AlbertGBarber/Pixel-Shades/Images/IMG_20191211_094721 (1).jpg

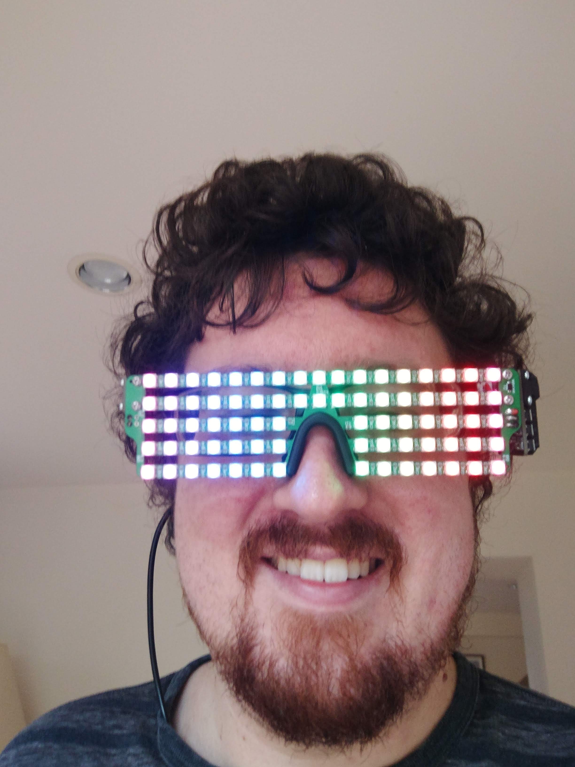
Images/IMG_20191211_094721 (1).jpg
