AlbertGBarber/Pixel-Shades/Images/Shades Back.jpg

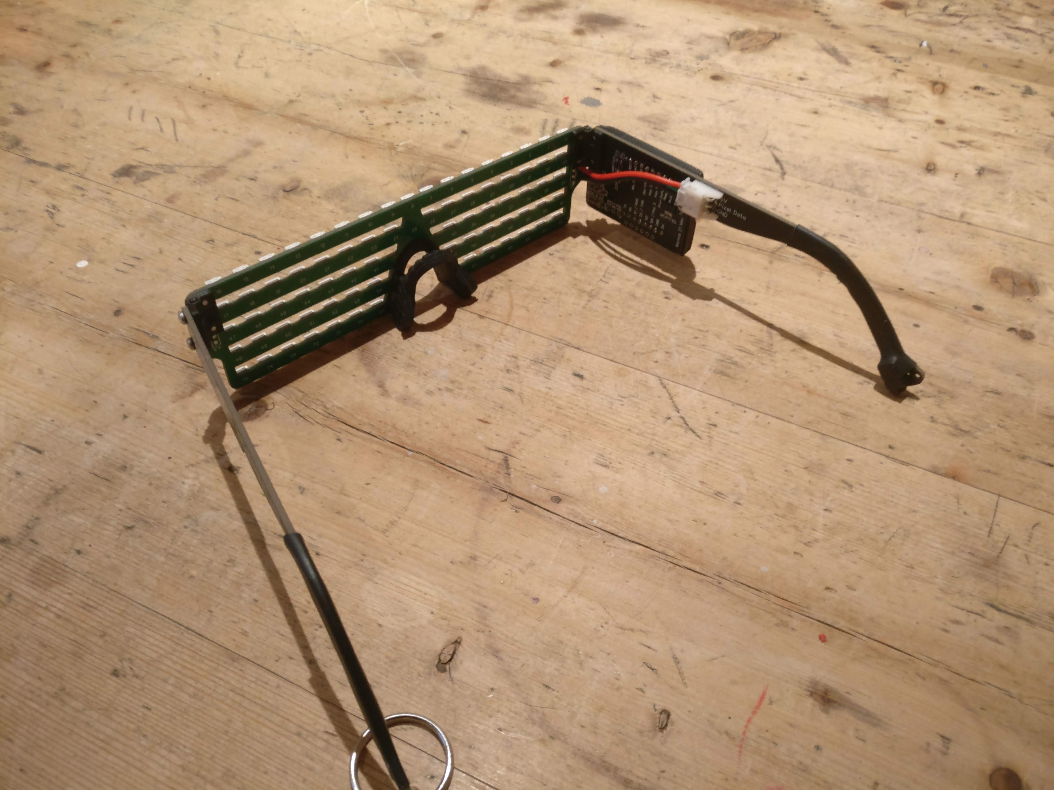
Images/Shades Back.jpg
