AlbertGBarber/Pixel-Shades/Images/Shades Cover.jpg

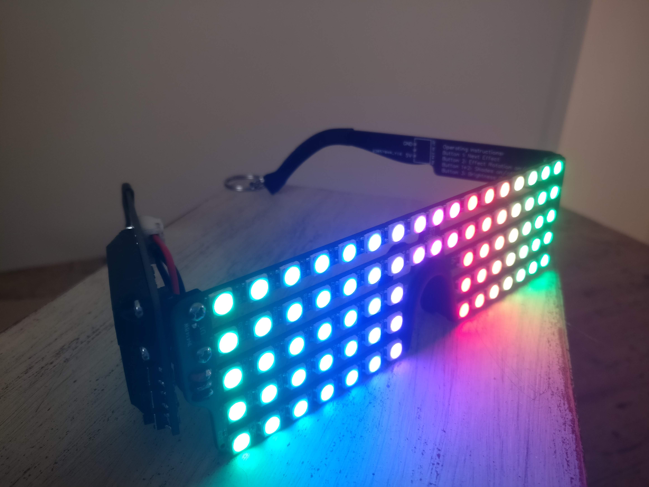
Images/Shades Cover.jpg
