AlbertGBarber/Pixel-Shades/Images/Shades PCBs and Power Bank.jpg

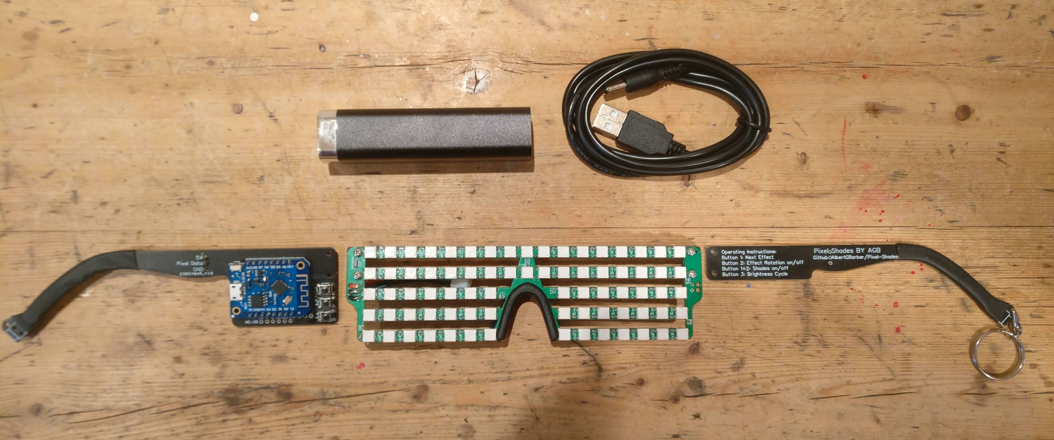
Images/Shades PCBs and Power Bank.jpg
