AlbertGBarber/Pixel-Shades/Images/Shades With Power Bank - Copy.jpg

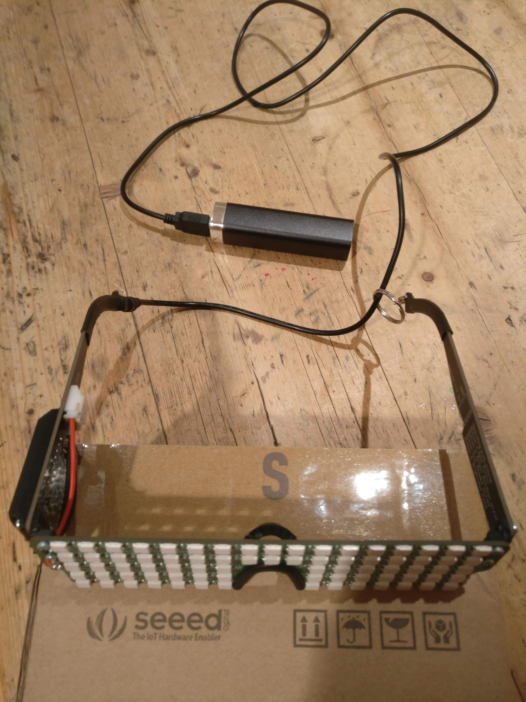
Images/Shades With Power Bank - Copy.jpg
