AlbertGBarber/Pixel-Shades/Images/PCB Ordering 2.PNG

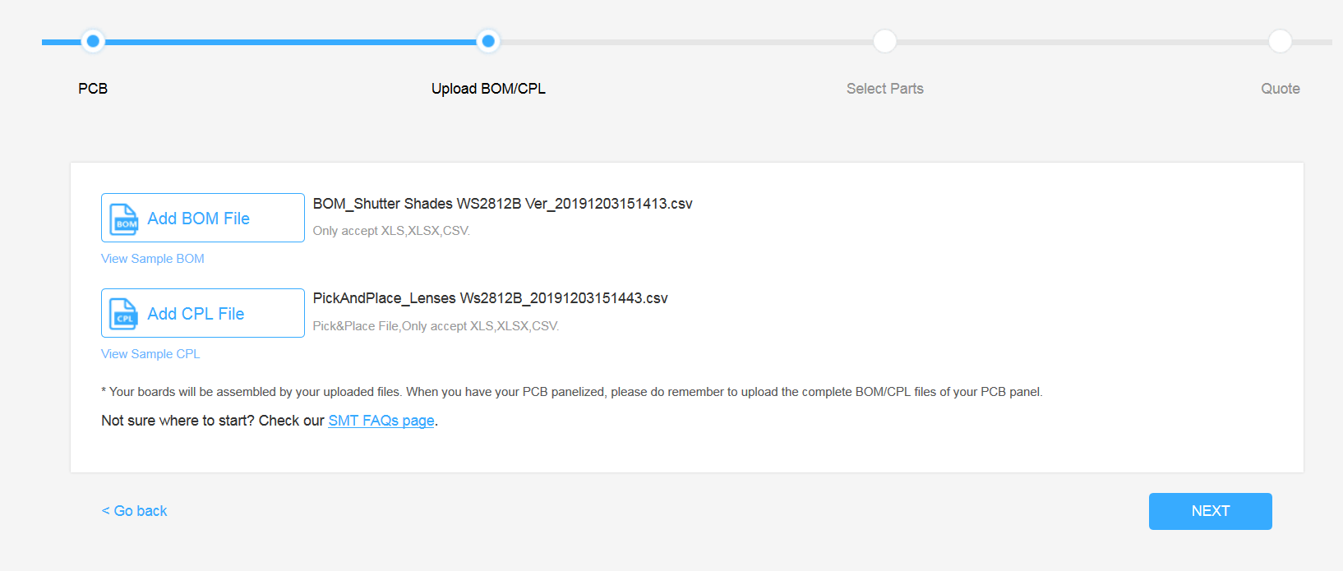
Images/PCB Ordering 2.PNG
