AlbertGBarber/Pixel-Shades/Images/PCB Ordering 4.PNG

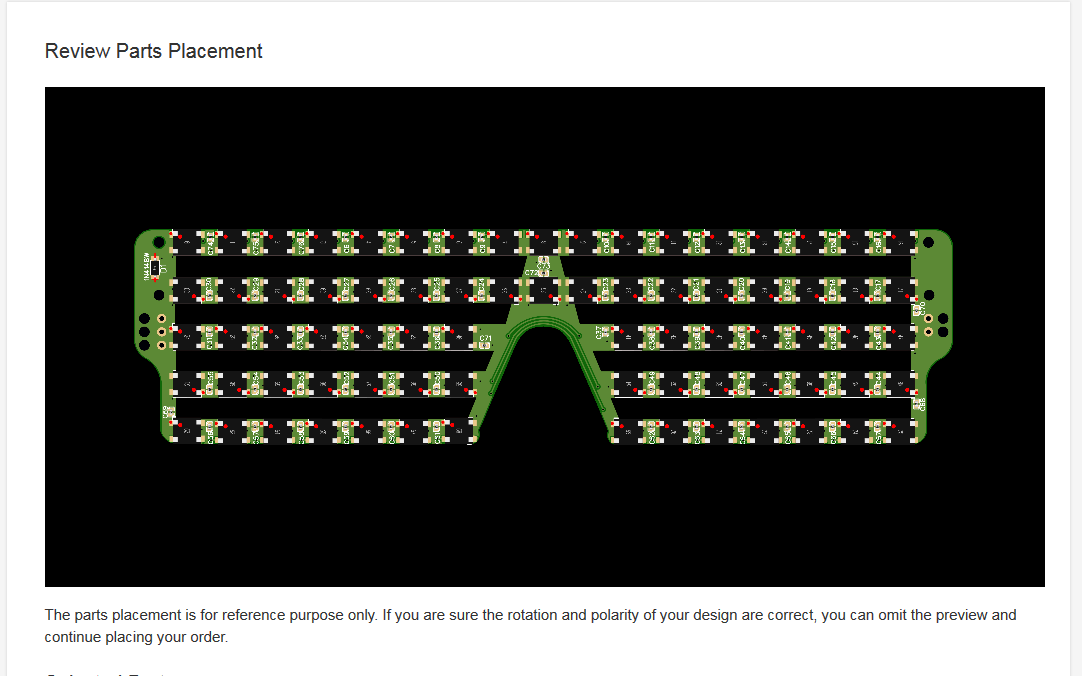
Images/PCB Ordering 4.PNG
