AlbertGBarber/Pixel-Shades/Images/Shades Final Assemble 1.jpg

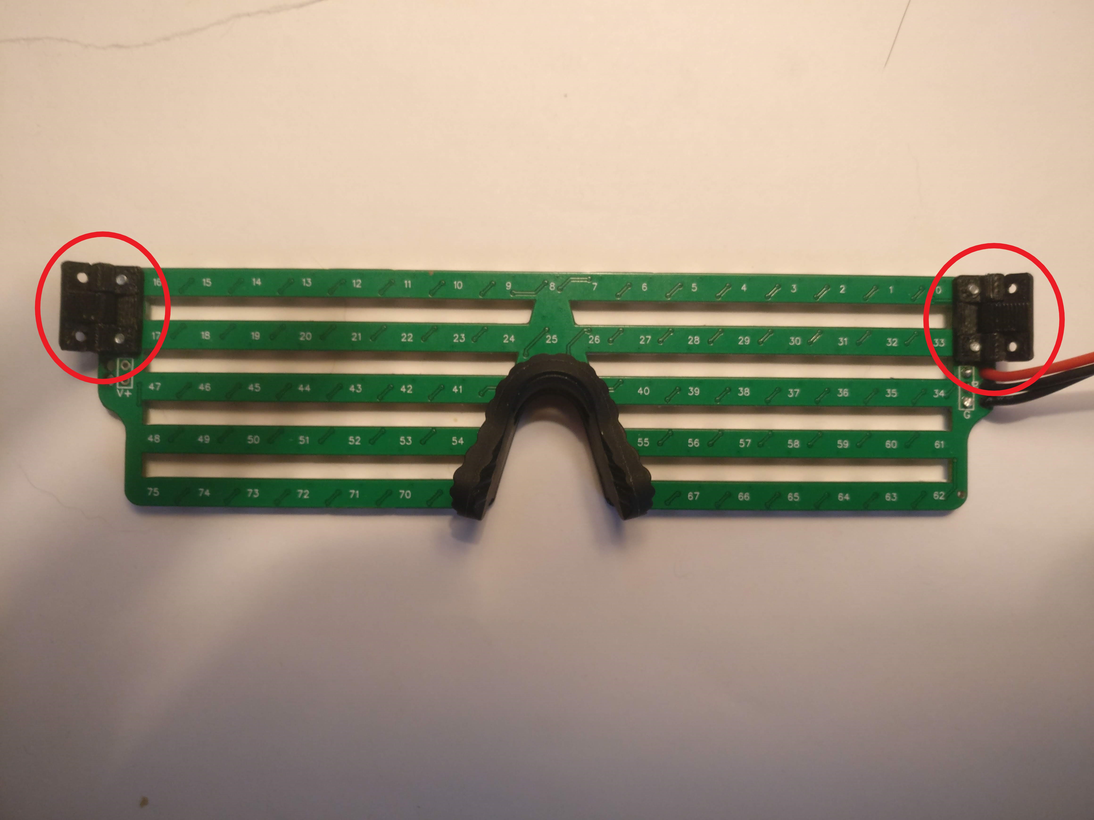
Images/Shades Final Assemble 1.jpg
