AlbertGBarber/Pixel-Shades/Images/Shades Final Assemble 2.jpg

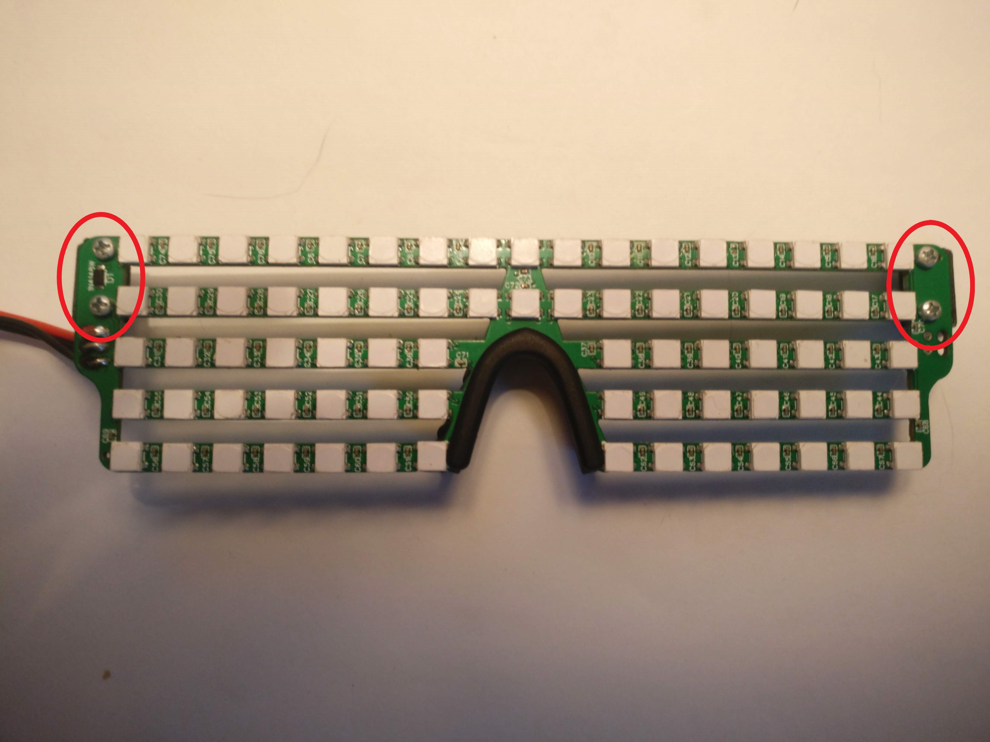
Images/Shades Final Assemble 2.jpg
