AlbertGBarber/Pixel-Shades/Images/Shades Final Assemble 3.jpg

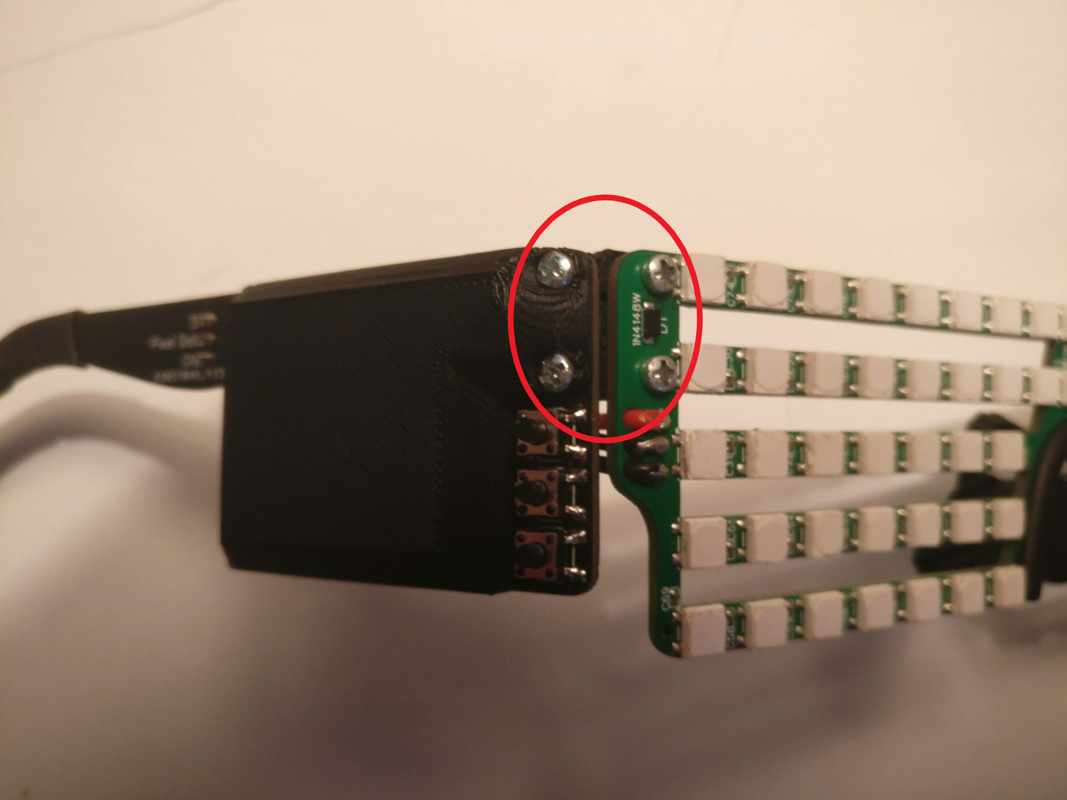
Images/Shades Final Assemble 3.jpg
