AlbertGBarber/Pixel-Shades/Images/Shades Final Assemble 5.jpg

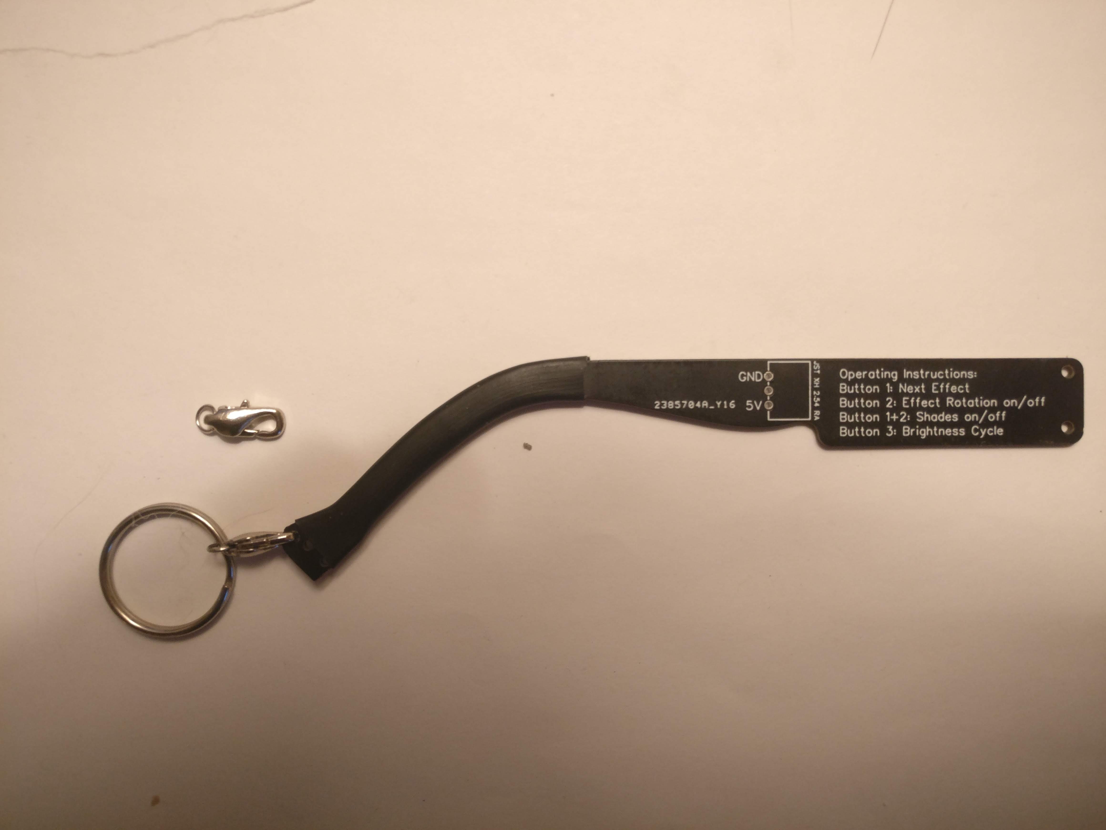
Images/Shades Final Assemble 5.jpg
