AlbertGBarber/Pixel-Shades/Images/Shades Final Assemble 6.jpg

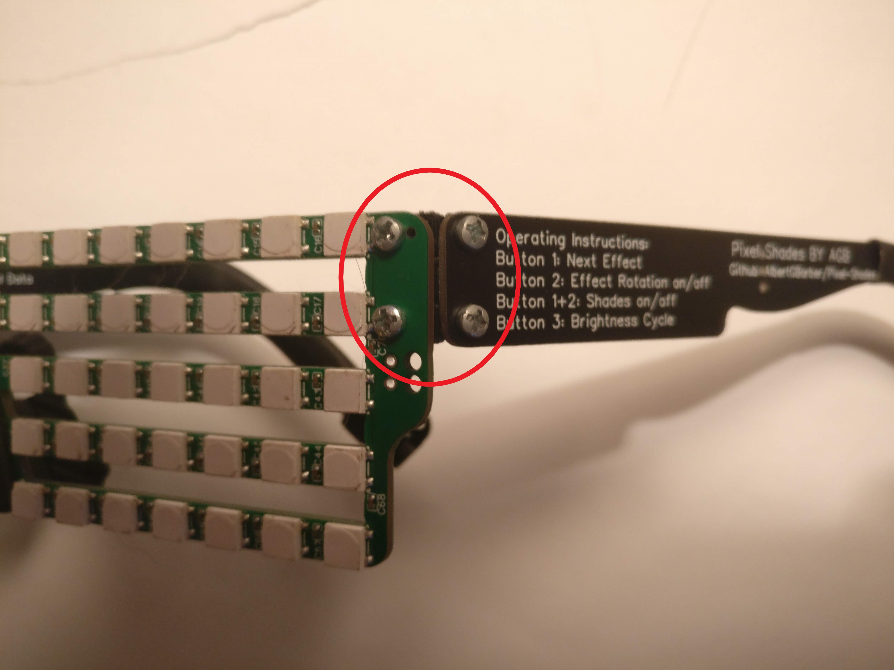
Images/Shades Final Assemble 6.jpg
