AlbertGBarber/Pixel-Shades/Images/Shades Final Assemble 8.PNG

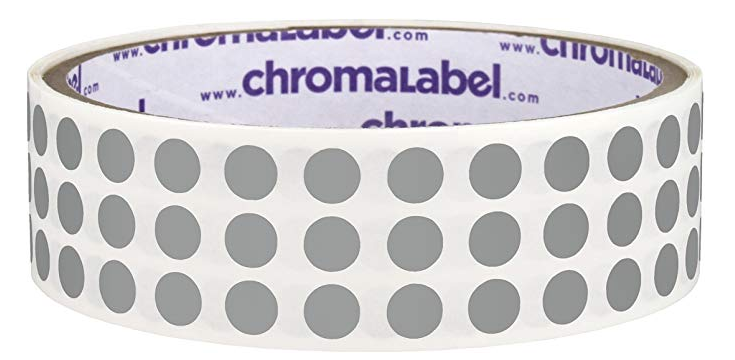
Images/Shades Final Assemble 8.PNG
