AlbertGBarber/Pixel-Shades/Images/Shades PCB Assembly 1.jpg

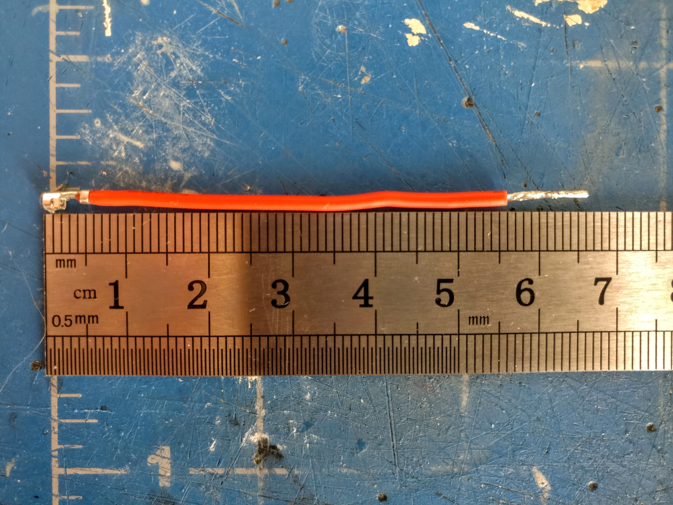
Images/Shades PCB Assembly 1.jpg
