AlbertGBarber/Pixel-Shades/Images/Shades PCB Assembly 2.jpg

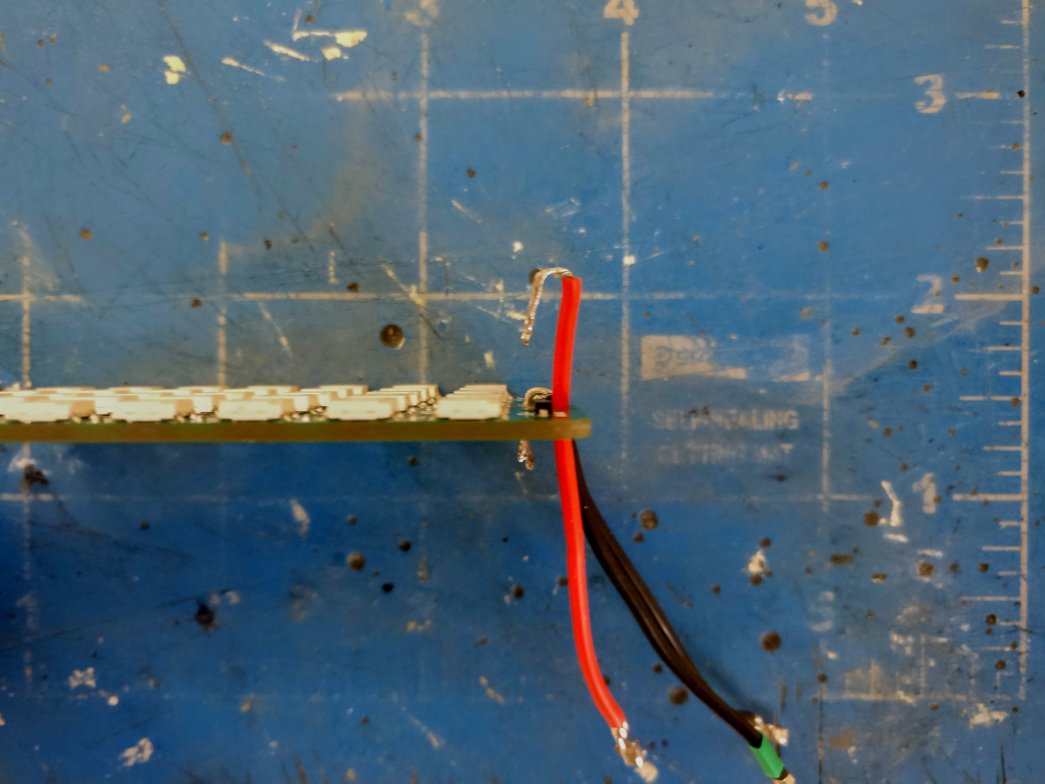
Images/Shades PCB Assembly 2.jpg
