AlbertGBarber/Pixel-Shades/Images/Shades PCB Assembly 3.jpg

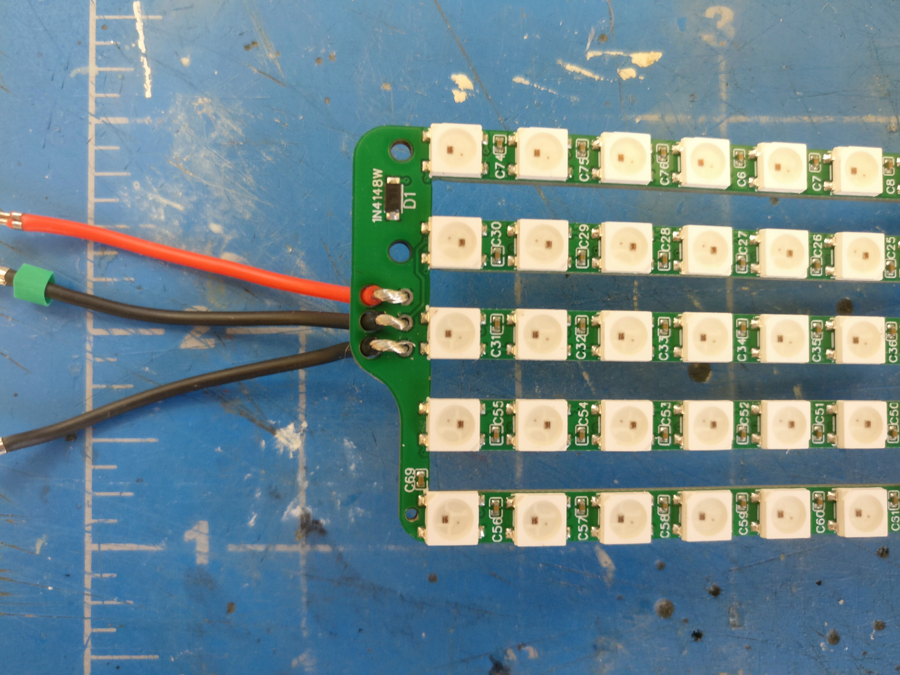
Images/Shades PCB Assembly 3.jpg
