AlbertGBarber/Pixel-Shades/Images/Shades PCB Assembly 4.jpg

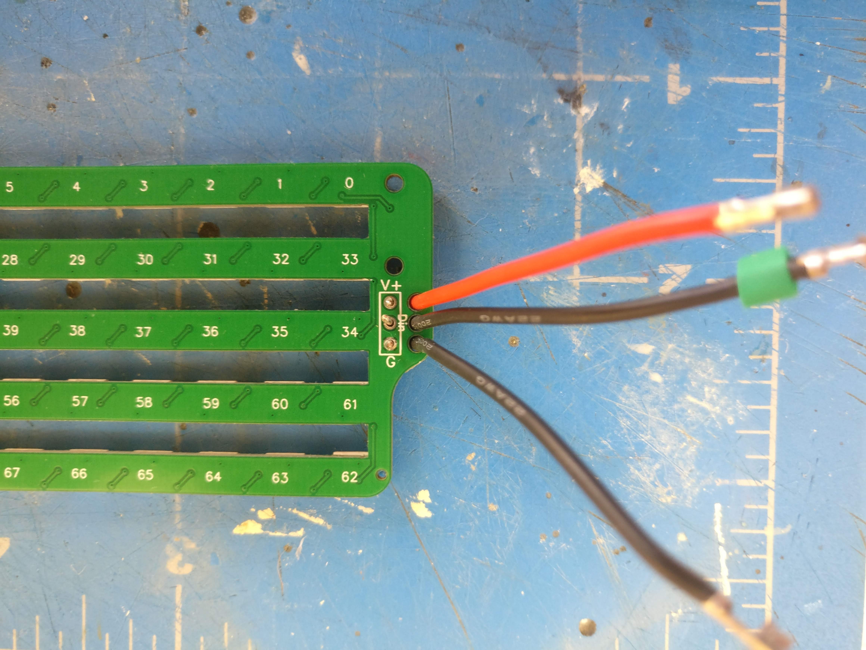
Images/Shades PCB Assembly 4.jpg
