AlbertGBarber/Pixel-Shades/Images/Shades PCB Assembly 5.jpg

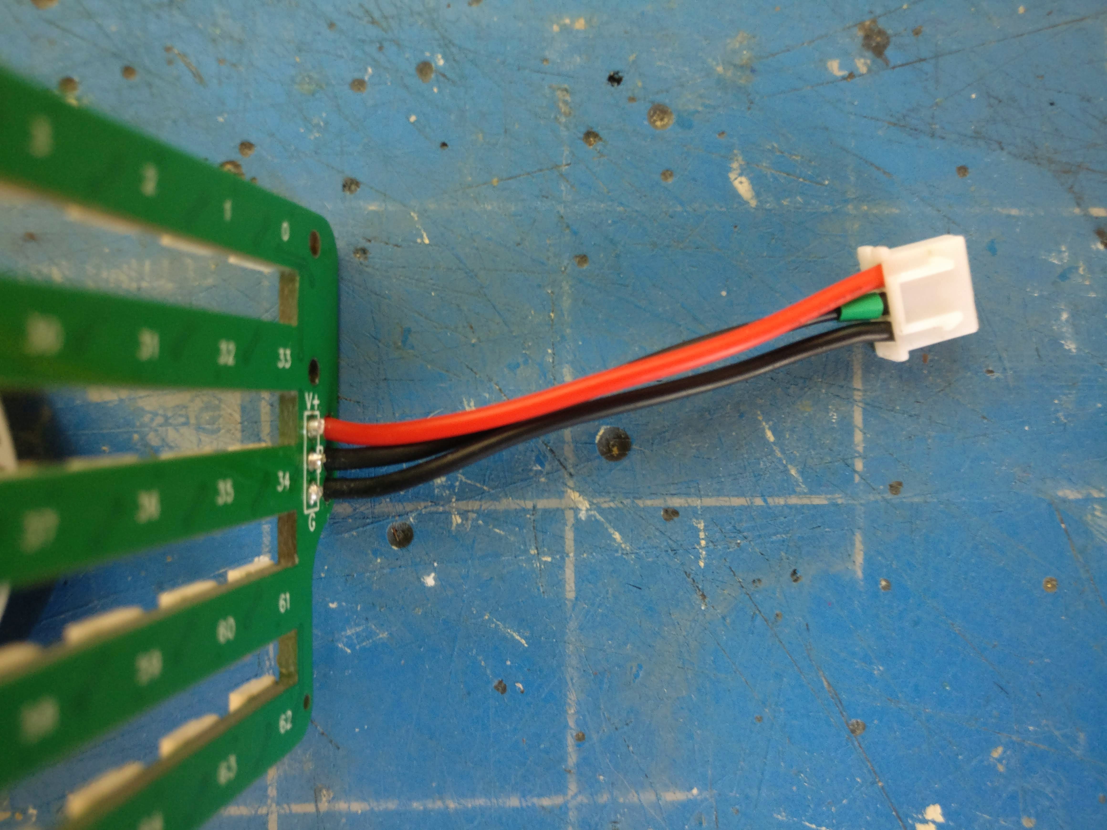
Images/Shades PCB Assembly 5.jpg
