AlbertGBarber/Pixel-Shades/Images/Temple PCB Assemble 1.jpg

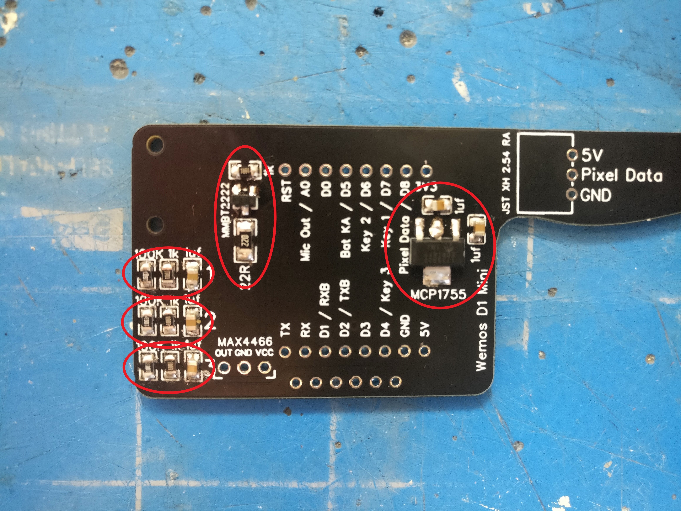
Images/Temple PCB Assemble 1.jpg
