AlbertGBarber/Pixel-Shades/Images/Temple PCB Assemble 3.jpg

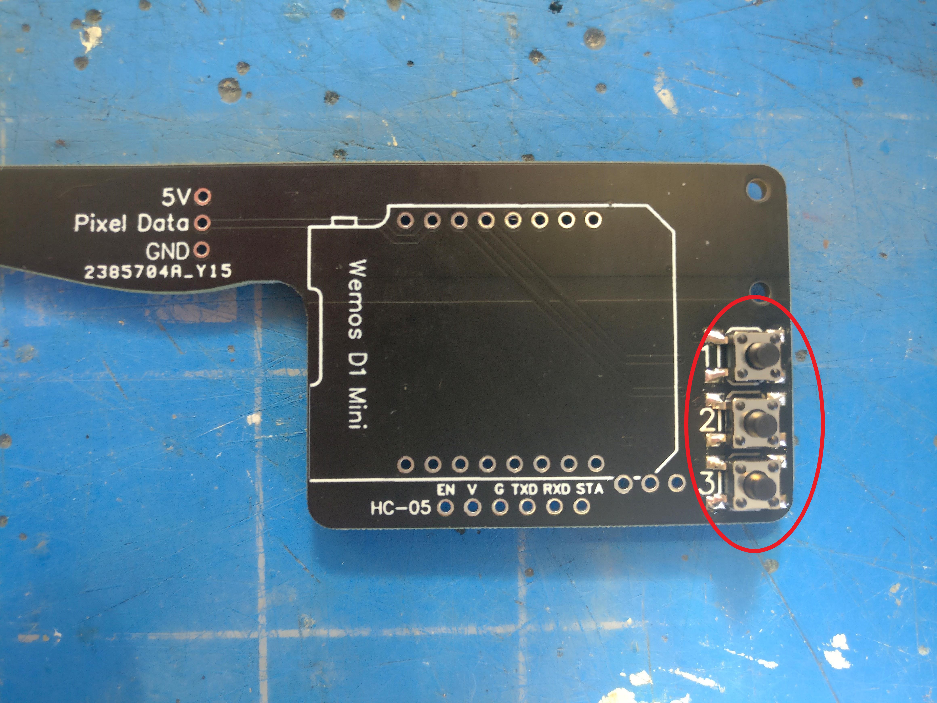
Images/Temple PCB Assemble 3.jpg
