AlbertGBarber/Pixel-Shades/Images/Temple PCB Assemble 4.jpg

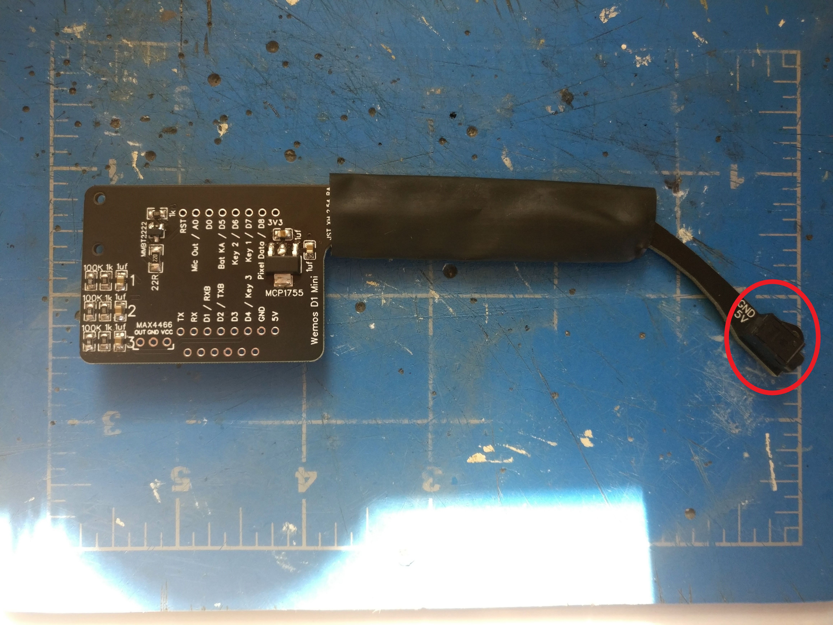
Images/Temple PCB Assemble 4.jpg
