AlbertGBarber/Pixel-Shades/Images/Temple PCB Assemble 5.jpg

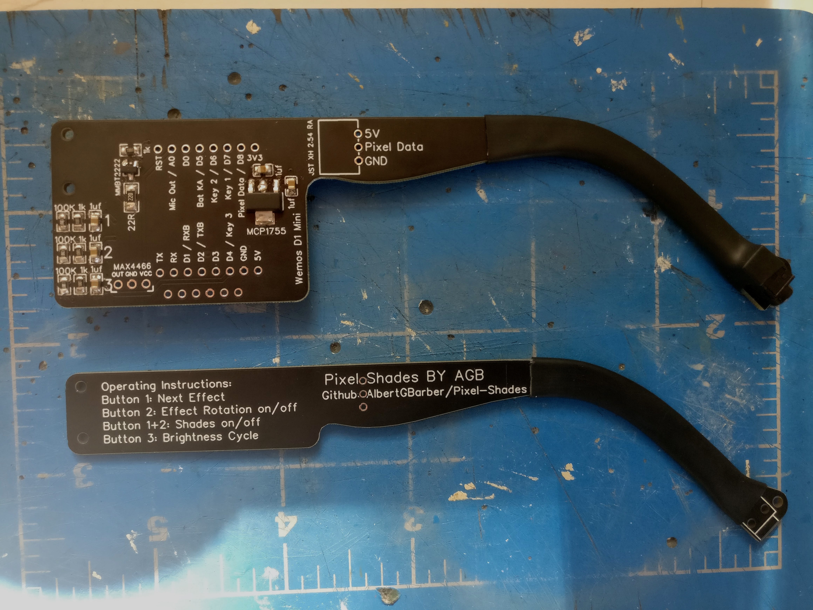
Images/Temple PCB Assemble 5.jpg
